OminousIndustries/peri/prints/Gearbox_Top.stl

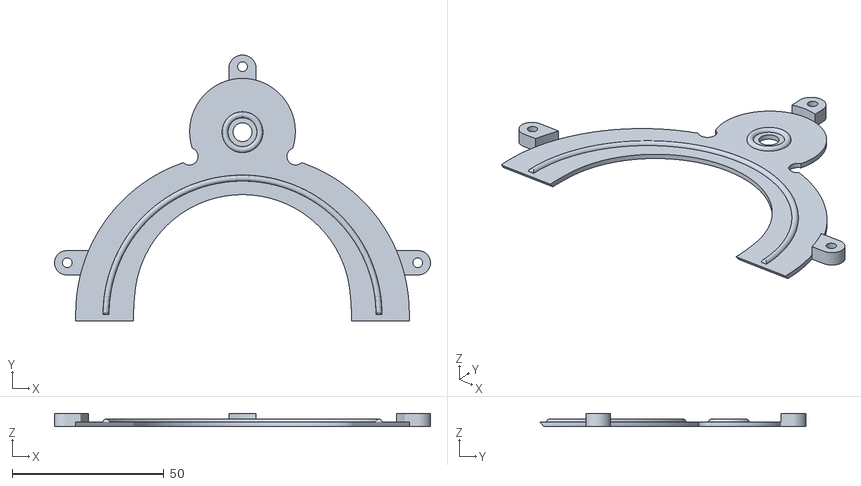
[picture p19: CAD file, 2026-10-10]
prints/Gearbox_Top.stl
124.0 x 87.7 x 4.40
