OminousIndustries/peri/prints/Gearbox_Mount_PRINT3X.stl

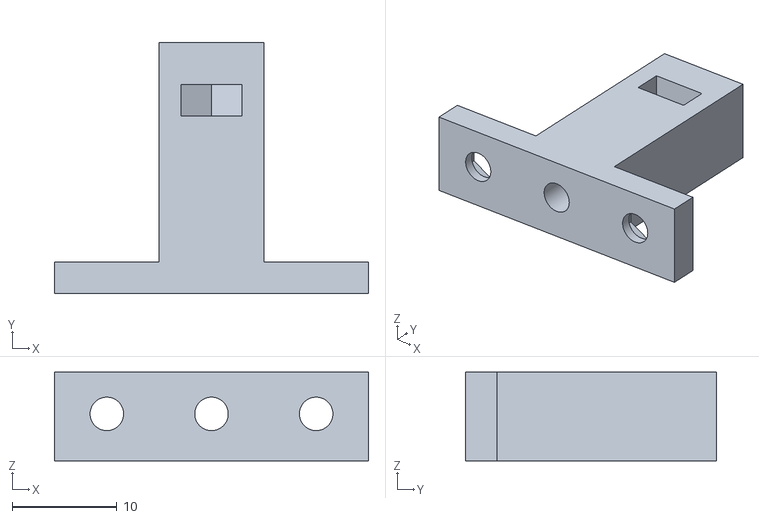
[picture p20: CAD file, 2026-10-10]
prints/Gearbox_Mount_PRINT3X.stl
30.0 x 24.0 x 8.50
